rekirxs/NeoXalle-Hardware/Images/IMG_3529.JPG

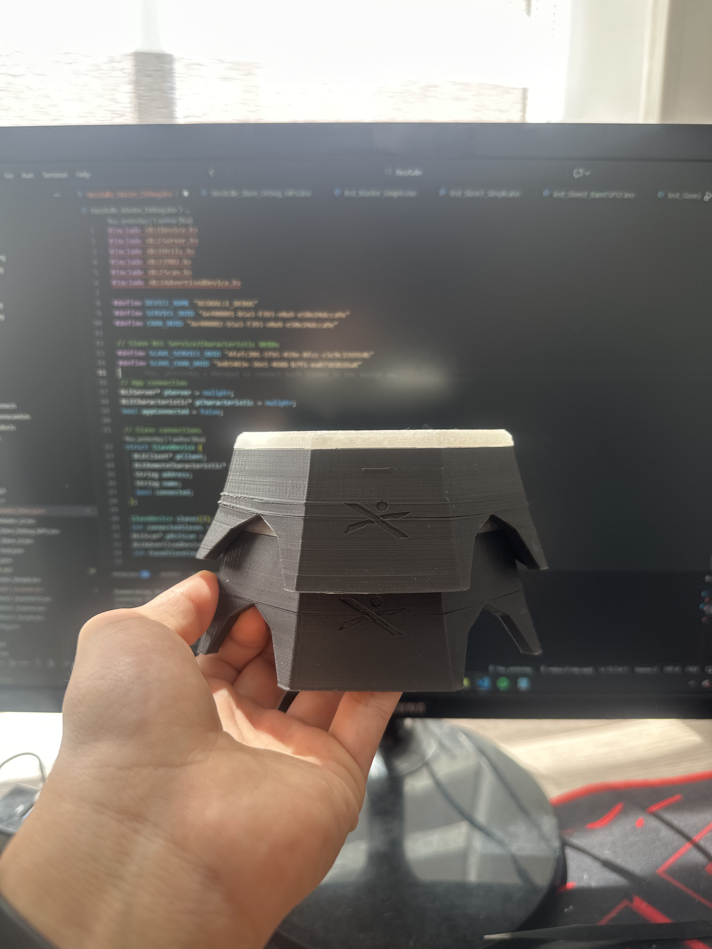
Images/IMG_3529.JPG
