rekirxs/NeoXalle-Hardware/Images/IMG_3926.JPG

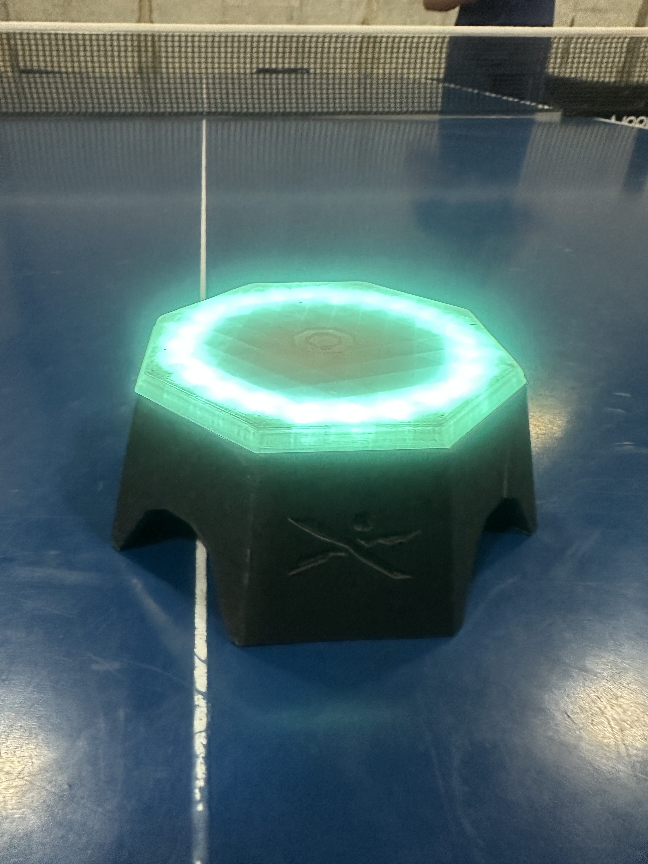
Images/IMG_3926.JPG
