rekirxs/NeoXalle-Hardware/schematic/Project.kicad_sch

## KiCad design schematic/Project.kicad_sch (2026-04-01)

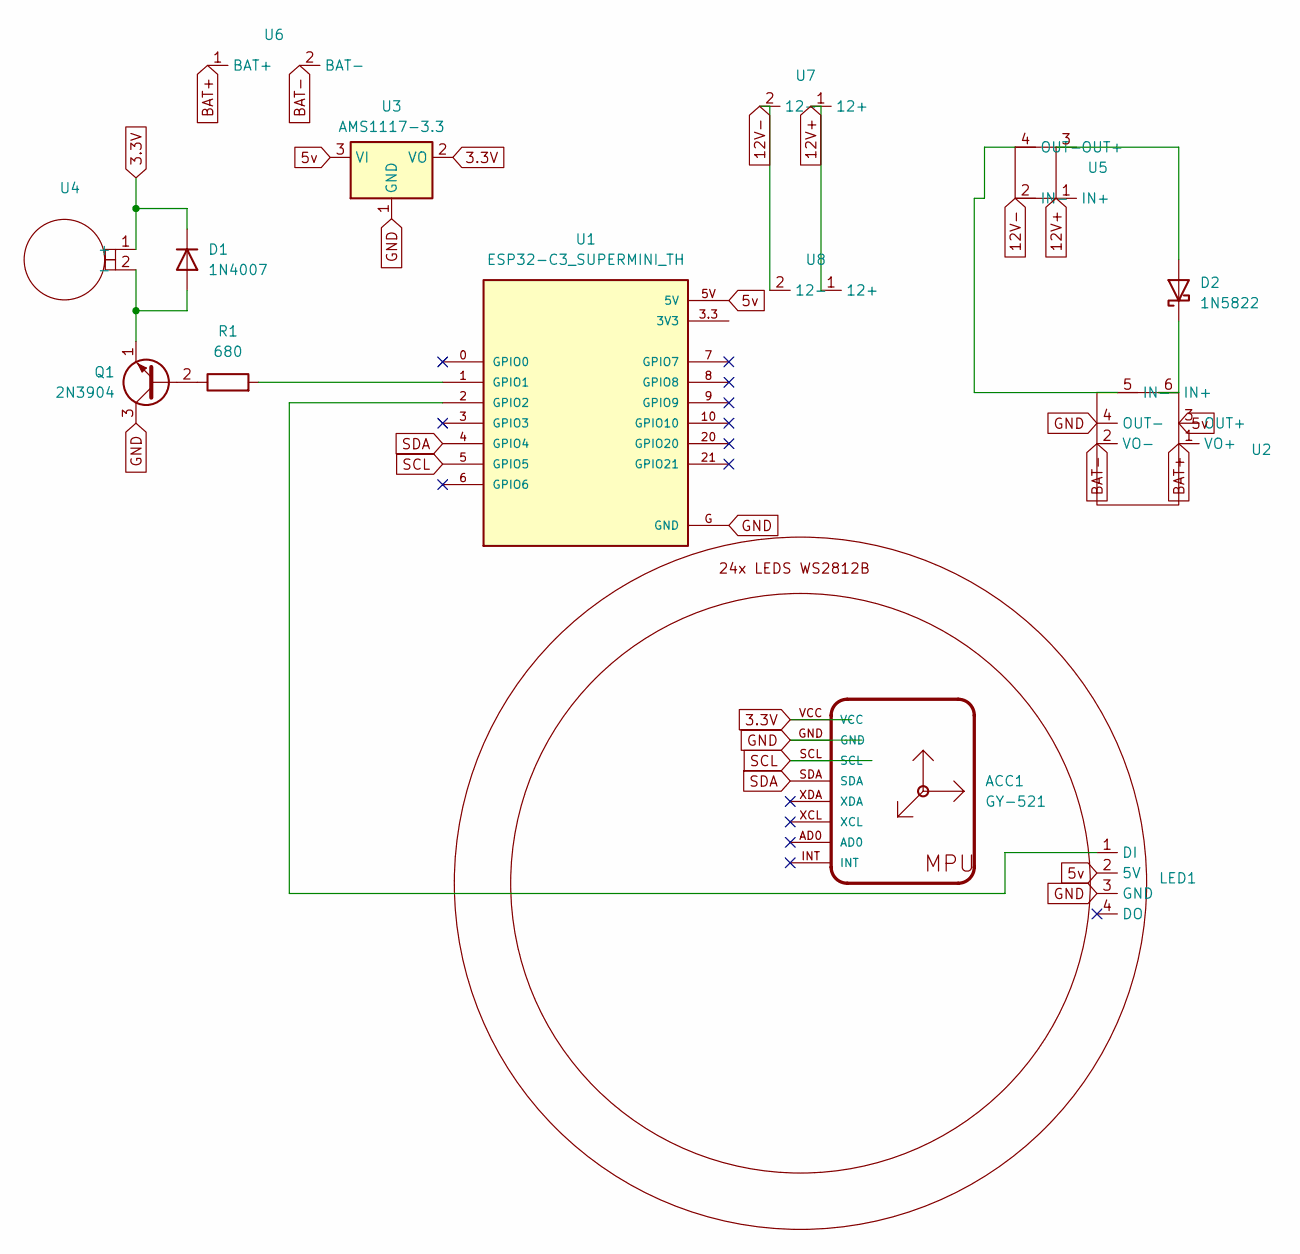
[picture p17: schematic Project.kicad_sch]

Parts:
ACC1: GY-521; MODULE_GY-521
D1: 1N4007; D_DO-41_SOD81_P10.16mm_Horizontal
D2: 1N5822; D_DO-201AD_P15.24mm_Horizontal
LED1: Untitled
Q1: 2N3904; TO-92_Inline
R1: 680; R_Axial_DIN0207_L6.3mm_D2.5mm_P10.16mm_Horizontal
U1: ESP32-C3_SUPERMINI_TH; MODULE_ESP32-C3_SUPERMINI_TH
U2: ModuleCharger
U3: AMS1117-3.3; SOT-223-3_TabPin2
U4: Motor
U5: Module
U6: Battery_Input
U7, U8: PogoInput

Connections:
3.3V: ACC1.VCC, D1.1 (K), U3.2 (VO), U4.1 (+)
5v: LED1.2 (5V), U1.5V, U2.3 (OUT+), U3.3 (VI)
12V+: U5.1 (IN+), U7.1 (12+), U8.1 (12+)
12V-: U5.2 (IN-), U7.2 (12-), U8.2 (12-)
BAT+: U2.1 (VO+), U6.1 (BAT+)
BAT-: U2.2 (VO-), U6.2 (BAT-)
GND: ACC1.GND, LED1.3 (GND), Q1.3 (C), U1.G (GND), U2.4 (OUT-), U3.1 (GND)
unnamed: D1.2 (A), Q1.1 (E), U4.2 (-)
unnamed: D2.1 (K), U2.6 (IN+)
unnamed: D2.2 (A), U5.3 (OUT+)
unnamed: LED1.1 (DI), U1.2 (GPIO2)
unnamed: Q1.2 (B), R1.1
unnamed: R1.2, U1.1 (GPIO1)
unnamed: U2.5 (IN-), U5.4 (OUT-)
SCL: ACC1.SCL, U1.5 (GPIO5)
SDA: ACC1.SDA, U1.4 (GPIO4)
